AureleJ/SyncFloraPot/firmware/src/drivers/moisture/moisture.c

#include "moisture.h"
#include "esp_adc/adc_oneshot.h"
#include "esp_log.h"
#include "../adc_manager/adc_manager.h"
#include "freertos/FreeRTOS.h"

static const char *TAG = "MOISTURE_DRIVER";
static adc_channel_t moisture_adc_channel = -1;
static gpio_num_t moisture_power_pin = -1;
static bool s_initialized = false;
static const int ADC_MAX_VALUE = 4095;
static const int NUM_READINGS = 20;

esp_err_t moisture_init(adc_channel_t adc_channel, gpio_num_t power_pin)
{
    moisture_adc_channel = adc_channel;
    moisture_power_pin = power_pin;

    gpio_reset_pin(moisture_power_pin);

    adc_oneshot_unit_handle_t adc_handle = adc_manager_get_handle();

    adc_oneshot_chan_cfg_t chan_config = {
        .atten = ADC_ATTEN_DB_12,
        .bitwidth = ADC_BITWIDTH_12,
    };

    esp_err_t ret = adc_oneshot_config_channel(adc_handle, moisture_adc_channel, &chan_config);
    if (ret != ESP_OK)
    {
        ESP_LOGE(TAG, "ADC channel config failed: %s", esp_err_to_name(ret));
        return ret;
    }

    ret = gpio_set_direction(moisture_power_pin, GPIO_MODE_OUTPUT);
    if (ret != ESP_OK)
    {
        ESP_LOGE(TAG, "Failed to set power pin direction: %s", esp_err_to_name(ret));
        return ret;
    }

    ret = gpio_set_level(moisture_power_pin, 0);
    if (ret != ESP_OK)
    {
        ESP_LOGE(TAG, "Failed to set power pin level: %s", esp_err_to_name(ret));
        return ret;
    }

    s_initialized = true;

    return ESP_OK;
}

int moisture_read_percent(void)
{
    if (!s_initialized)
    {
        ESP_LOGE(TAG, "Moisture sensor not initialized");
        return -1;
    }

    esp_err_t ret = gpio_set_level(moisture_power_pin, 1);
    if (ret != ESP_OK)
    {
        ESP_LOGE(TAG, "Failed to set power pin level: %s", esp_err_to_name(ret));
        return -1;
    }

    adc_oneshot_unit_handle_t adc_handle = adc_manager_get_handle();

    int total = 0;
    int last_raw = 0;
    for (int i = 0; i < NUM_READINGS; i++)
    {
        int raw = 0;
        esp_err_t ret = adc_oneshot_read(adc_handle, moisture_adc_channel, &raw);
        if (ret != ESP_OK)
        {
            ESP_LOGE(TAG, "ADC read failed: %s", esp_err_to_name(ret));
            return -1;
        }

        if (raw < 0 || raw > ADC_MAX_VALUE)
            continue;

        if (last_raw != 0 && (raw < last_raw / 2 || raw > last_raw * 2))
            continue;

        total += raw;
    }

    ret = gpio_set_level(moisture_power_pin, 0);
    if (ret != ESP_OK)
    {
        ESP_LOGE(TAG, "Failed to set power pin level: %s", esp_err_to_name(ret));
        return -1;
    }

    int average = total / NUM_READINGS;
    return (average * 100) / ADC_MAX_VALUE;
}
